Jun-yong-lee/Omok_robot/goboard_point_detect/result/img.jpg

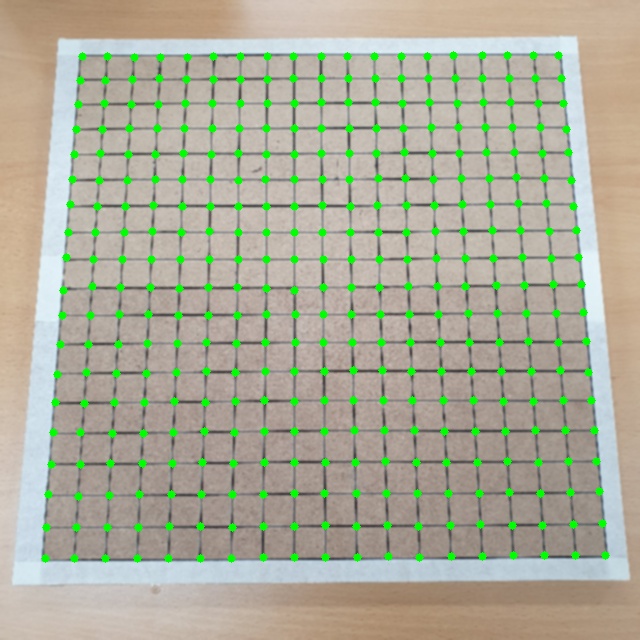
goboard_point_detect/result/img.jpg
