Jun-yong-lee/Omok_robot/goboard_point_detect/result/labeled_in_order.jpg

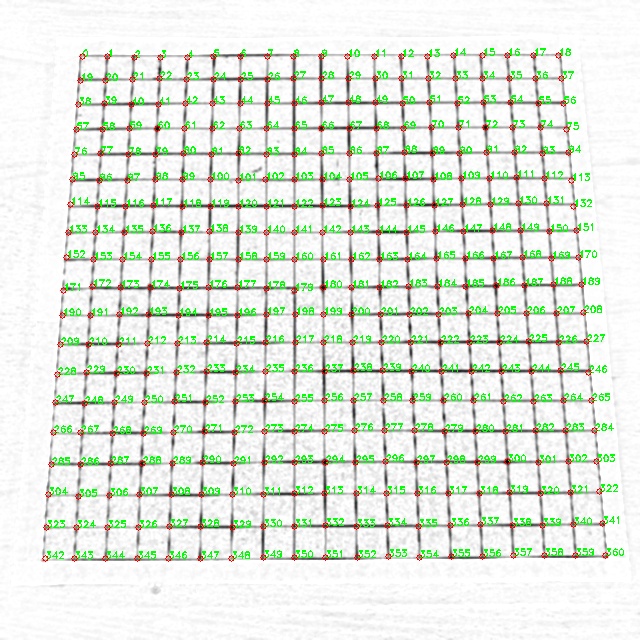
goboard_point_detect/result/labeled_in_order.jpg
