Jun-yong-lee/Omok_robot/goboard_point_detect/goboard2.jpg

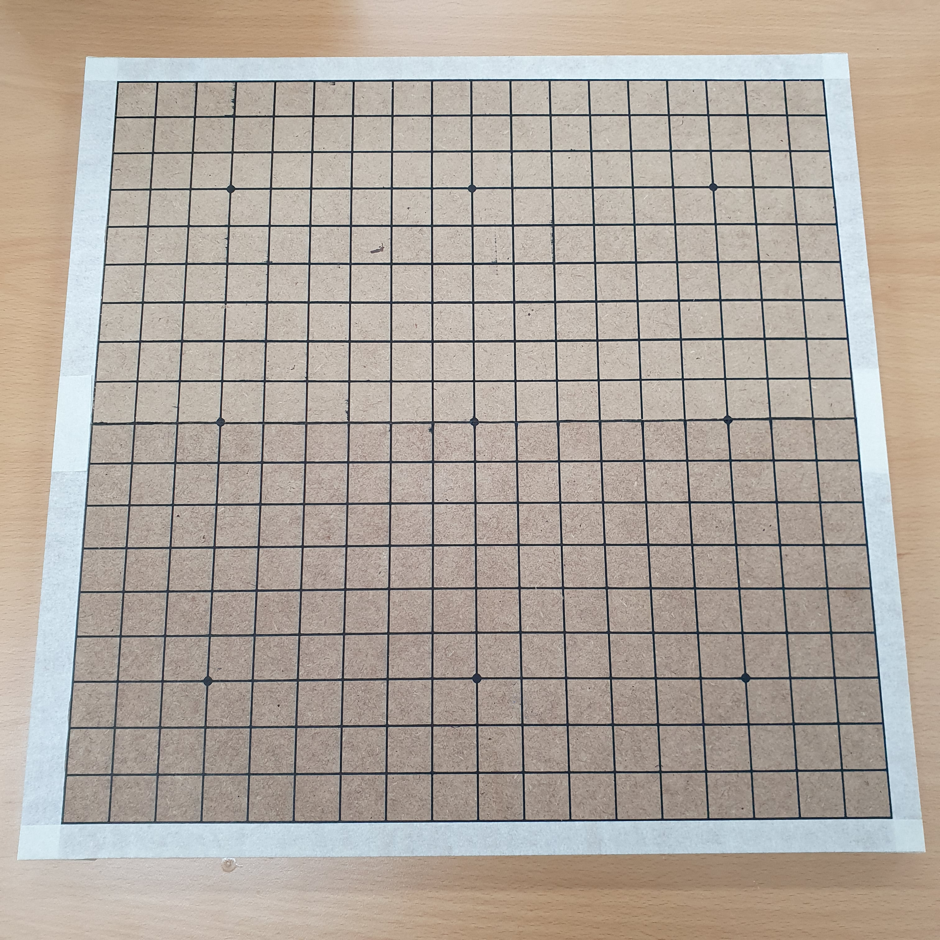
goboard_point_detect/goboard2.jpg
