Jun-yong-lee/Omok_robot/design_board_box/치수 늘린 모터 케이스/치수_solenoide fixed line.SLDPRT

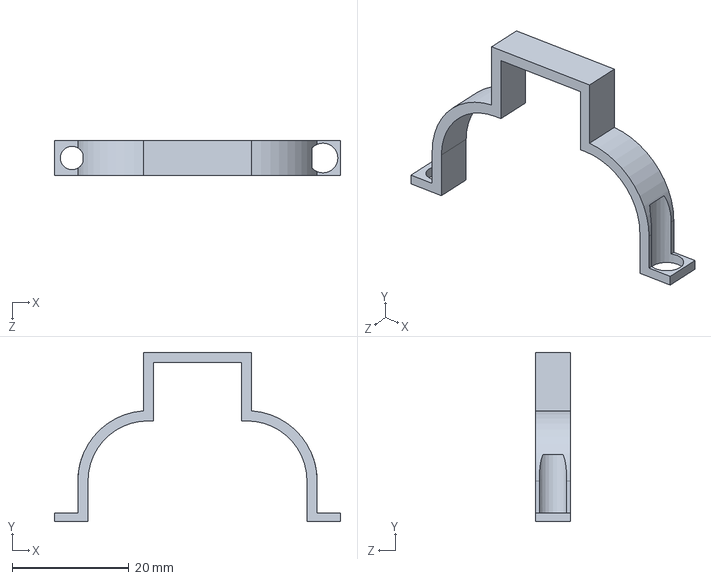
[picture p18: CAD file, 2022-11-21, last stored version]
design_board_box/치수 늘린 모터 케이스/치수_solenoide fixed line.SLDPRT
49.0 x 29.0 x 6.00 mm
