Jun-yong-lee/Omok_robot/design_dispenser/알.SLDPRT

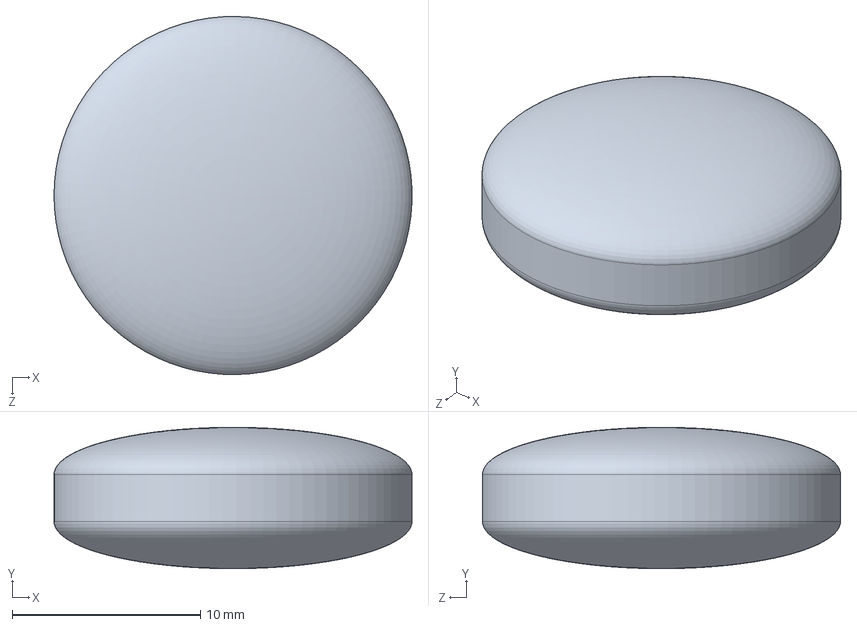
[picture p19: CAD file, 2022-11-21, last stored version]
design_dispenser/알.SLDPRT
19.0 x 7.50 x 19.0 mm
