Jun-yong-lee/Omok_robot/design_place/Profile link.SLDPRT

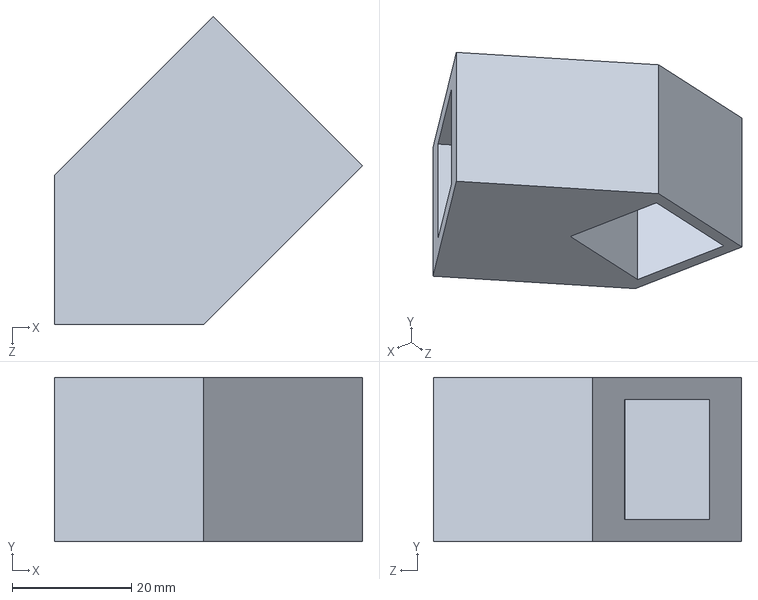
[picture p20: CAD file, 2022-11-21, last stored version]
design_place/Profile link.SLDPRT
51.6 x 27.5 x 51.6 mm
