Jun-yong-lee/Omok_robot/design_place/DP2020_420mm.SLDPRT

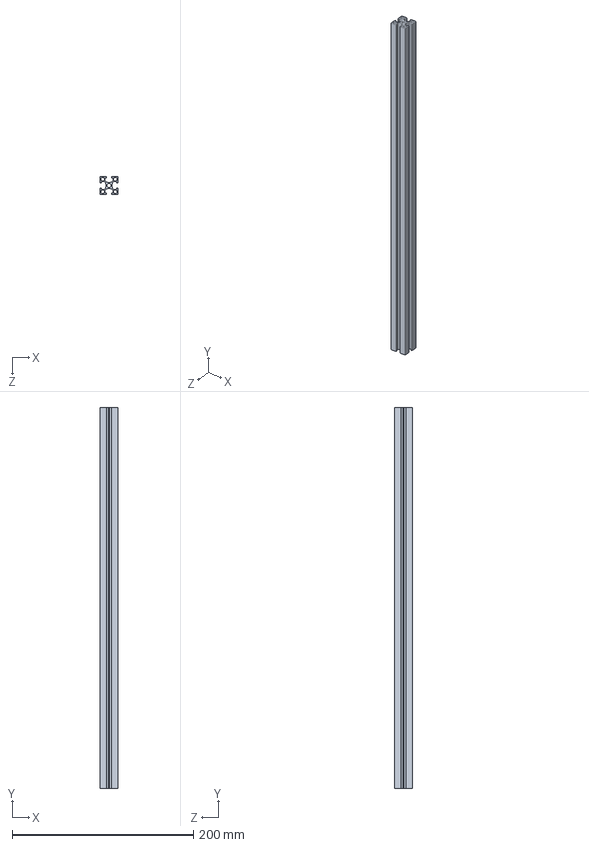
[picture p21: CAD file, 2022-11-21, last stored version]
design_place/DP2020_420mm.SLDPRT
20.0 x 420.0 x 20.0 mm
