Jun-yong-lee/Omok_robot/design_board_box/Vacuum Pump case 상.SLDPRT

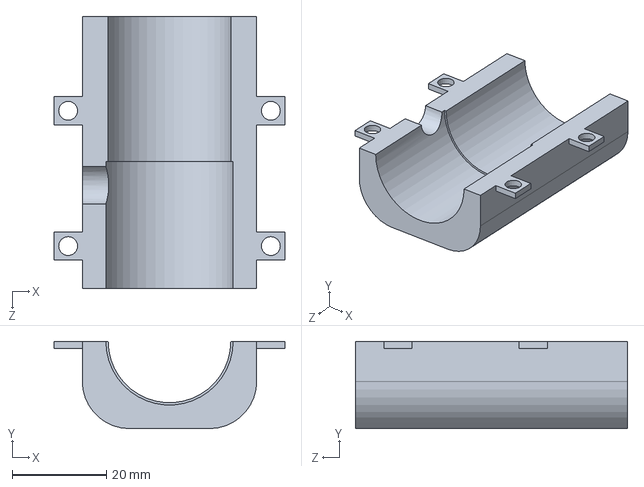
[picture p22: CAD file, 2022-11-21, last stored version]
design_board_box/Vacuum Pump case 상.SLDPRT
49.0 x 18.5 x 57.7 mm
