Jun-yong-lee/Omok_robot/design_dispenser/SG90.SLDPRT

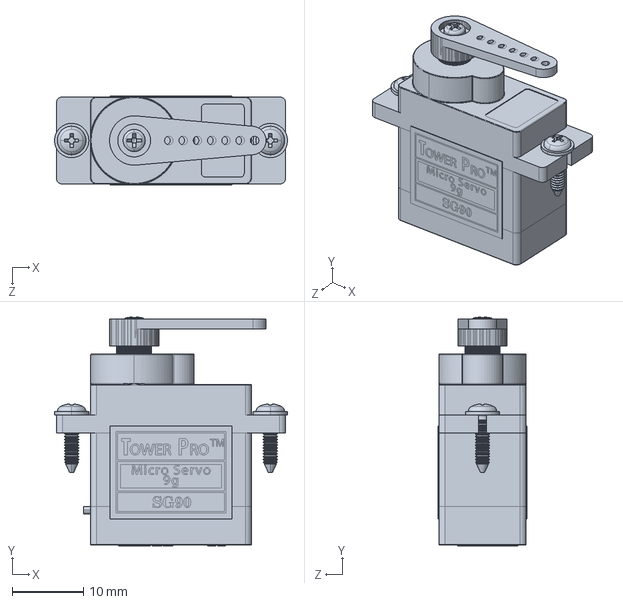
[picture p23: CAD file, 2022-11-21, last stored version]
design_dispenser/SG90.SLDPRT
32.6 x 32.0 x 12.4 mm
