Jun-yong-lee/Omok_robot/design_place/DP2020_510mm.SLDPRT

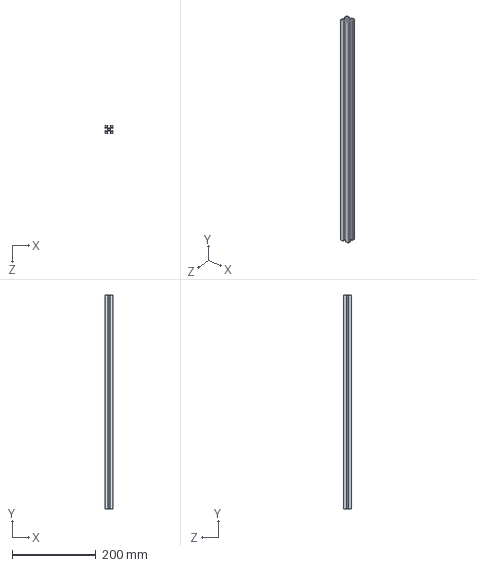
[picture p24: CAD file, 2022-11-21, last stored version]
design_place/DP2020_510mm.SLDPRT
20.0 x 510.0 x 20.0 mm
