Jun-yong-lee/Omok_robot/design_dispenser/Motor fixed flat.SLDPRT

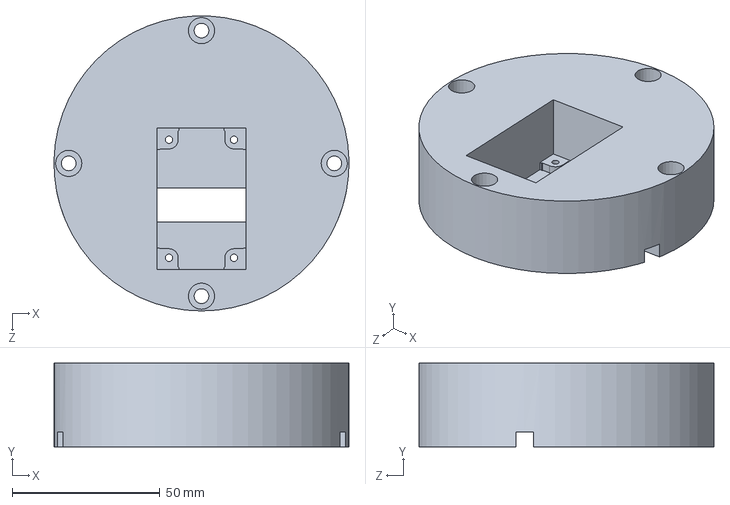
[picture p25: CAD file, 2022-11-21, last stored version]
design_dispenser/Motor fixed flat.SLDPRT
100.0 x 28.3 x 99.9 mm
