Jun-yong-lee/Omok_robot/design_place/Checkerboard.SLDPRT

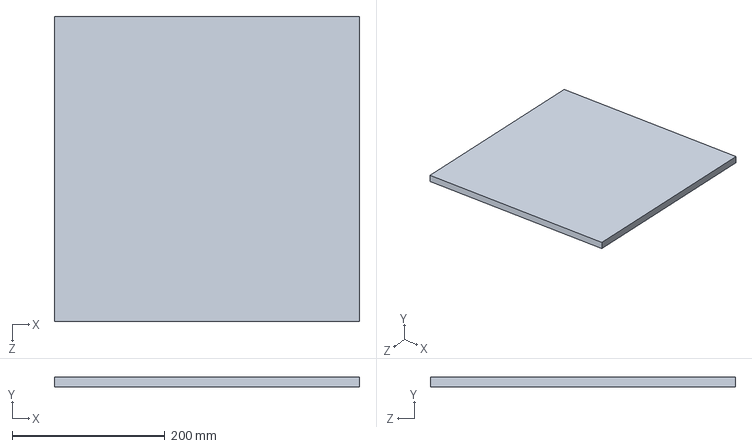
[picture p26: CAD file, 2022-11-21, last stored version]
design_place/Checkerboard.SLDPRT
400.0 x 13.0 x 400.0 mm
