Jun-yong-lee/Omok_robot/design_place/Cart.SLDPRT

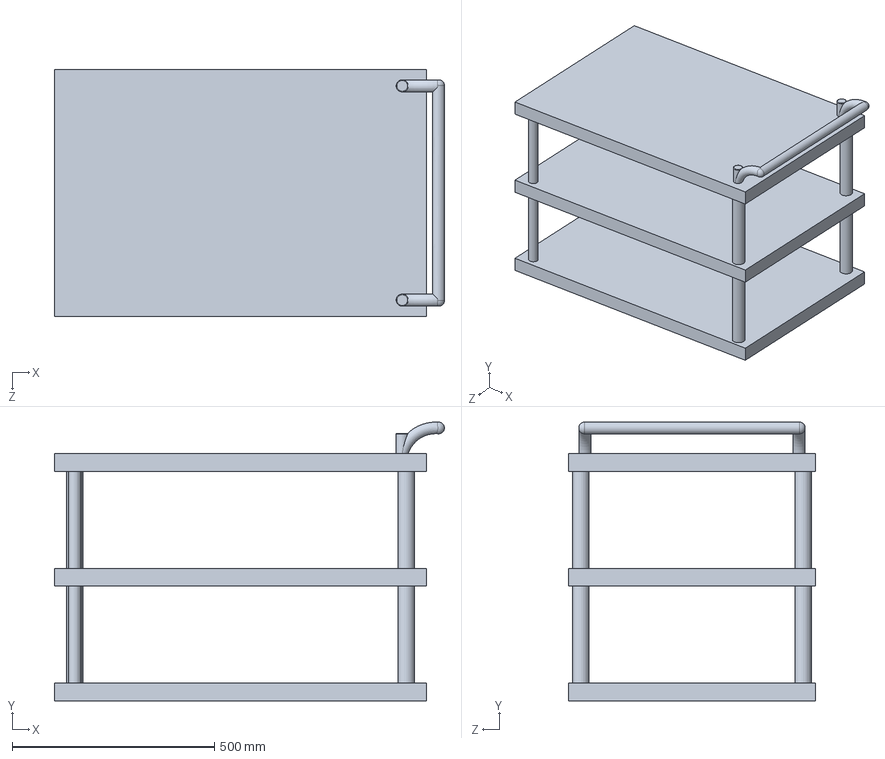
[picture p27: CAD file, 2022-11-21, last stored version]
design_place/Cart.SLDPRT
964.6 x 689.7 x 610.0 mm
