Jun-yong-lee/Omok_robot/design_board_box/solenoide.SLDPRT

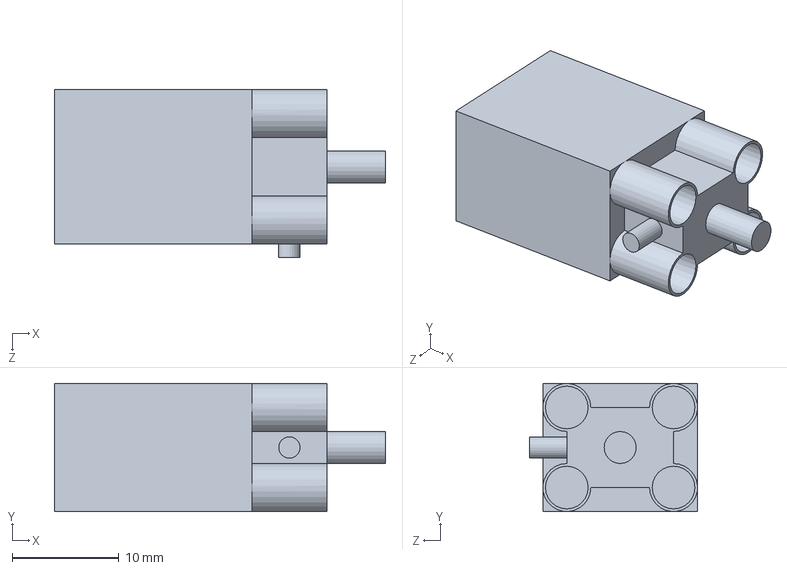
[picture p28: CAD file, 2022-11-21, last stored version]
design_board_box/solenoide.SLDPRT
31.0 x 12.0 x 15.8 mm
