Jun-yong-lee/Omok_robot/design_dispenser/오목알 경사각 증가 및 입구 확장.SLDPRT

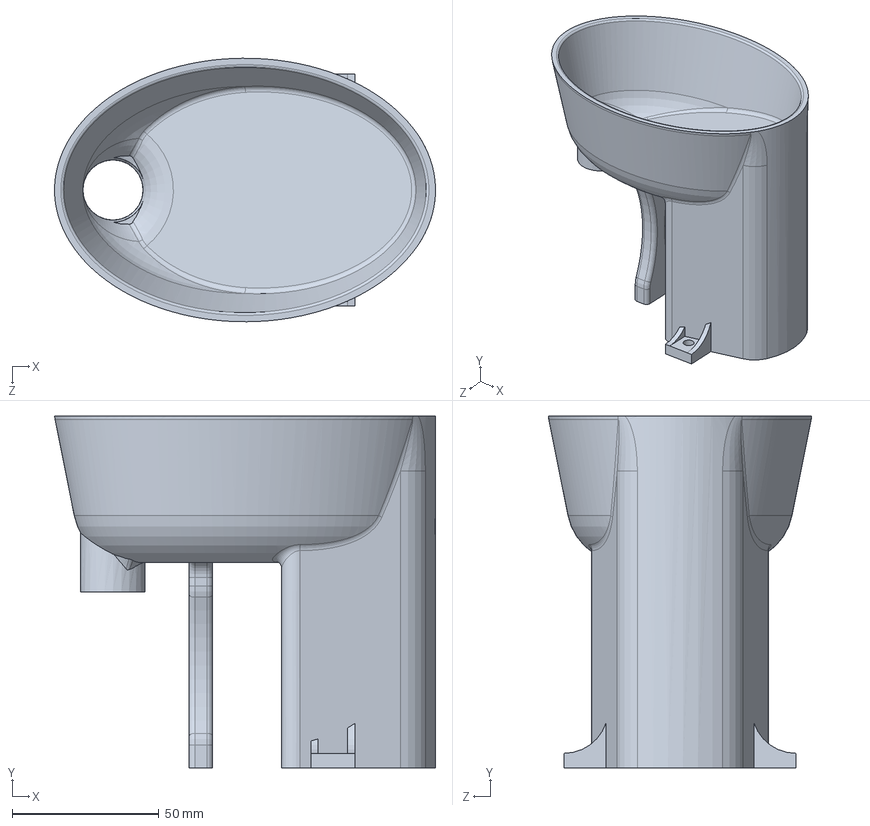
[picture p29: CAD file, 2022-11-21, last stored version]
design_dispenser/오목알 경사각 증가 및 입구 확장.SLDPRT
129.9 x 120.0 x 89.9 mm
