Jun-yong-lee/Omok_robot/design_place/DP2020_200mm.SLDPRT

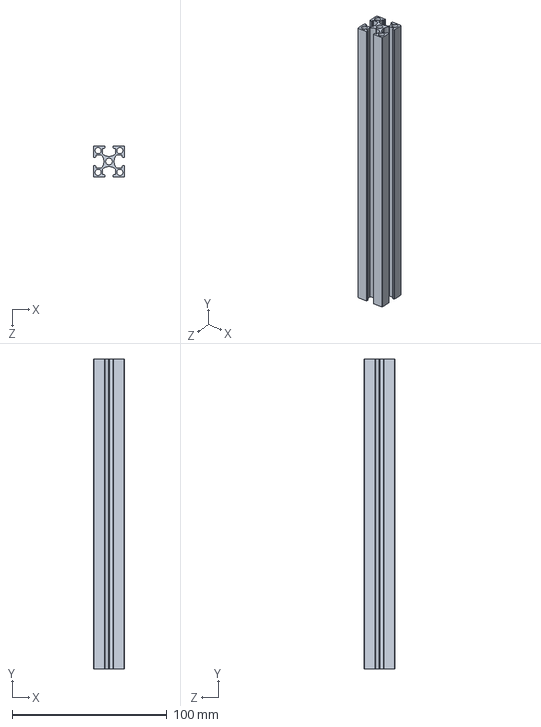
[picture p30: CAD file, 2022-11-21, last stored version]
design_place/DP2020_200mm.SLDPRT
20.0 x 200.0 x 20.0 mm
