Jun-yong-lee/Omok_robot/design_board_box/Vacuum Pump.SLDPRT

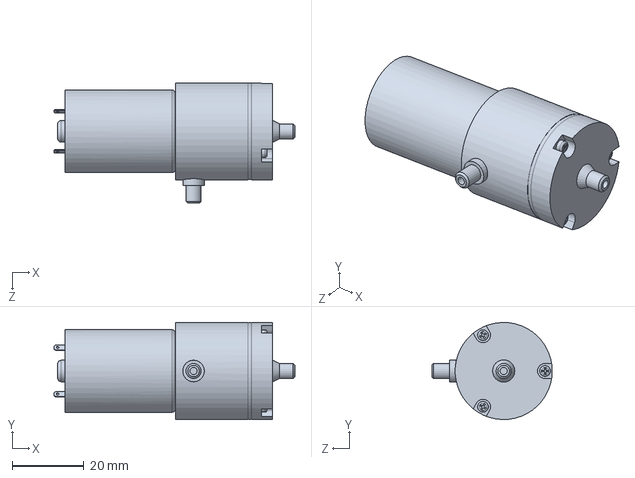
[picture p31: CAD file, 2022-11-21, last stored version]
design_board_box/Vacuum Pump.SLDPRT
67.0 x 27.0 x 33.5 mm
