Jun-yong-lee/Omok_robot/design_board_box/board support_L30.SLDPRT

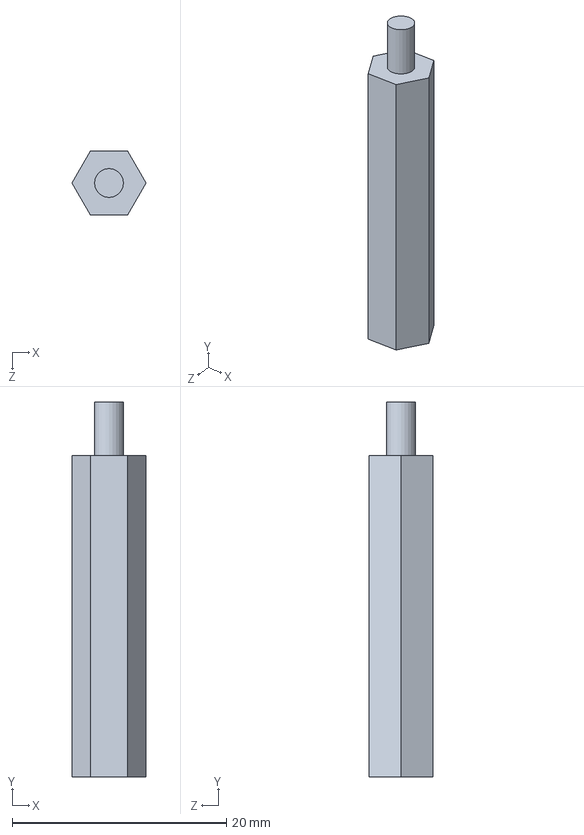
[picture p32: CAD file, 2022-11-21, last stored version]
design_board_box/board support_L30.SLDPRT
6.93 x 35.0 x 6.00 mm
