Jun-yong-lee/Omok_robot/design_board_box/Arduino uno.SLDPRT

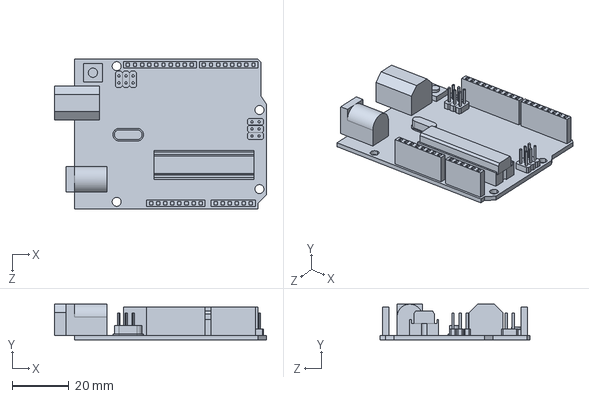
[picture p33: CAD file, 2022-11-21, last stored version]
design_board_box/Arduino uno.SLDPRT
75.0 x 12.6 x 53.0 mm
