Jun-yong-lee/Omok_robot/design_board_box/1 plate.SLDPRT

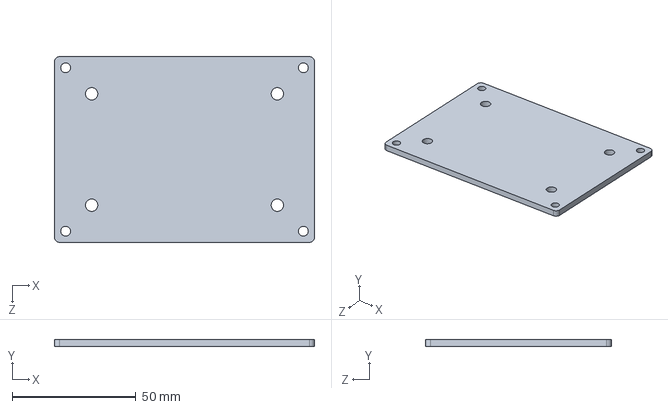
[picture p34: CAD file, 2022-11-21, last stored version]
design_board_box/1 plate.SLDPRT
105.0 x 3.00 x 75.0 mm
