Jun-yong-lee/Omok_robot/design_board_box/board support_L5.SLDPRT

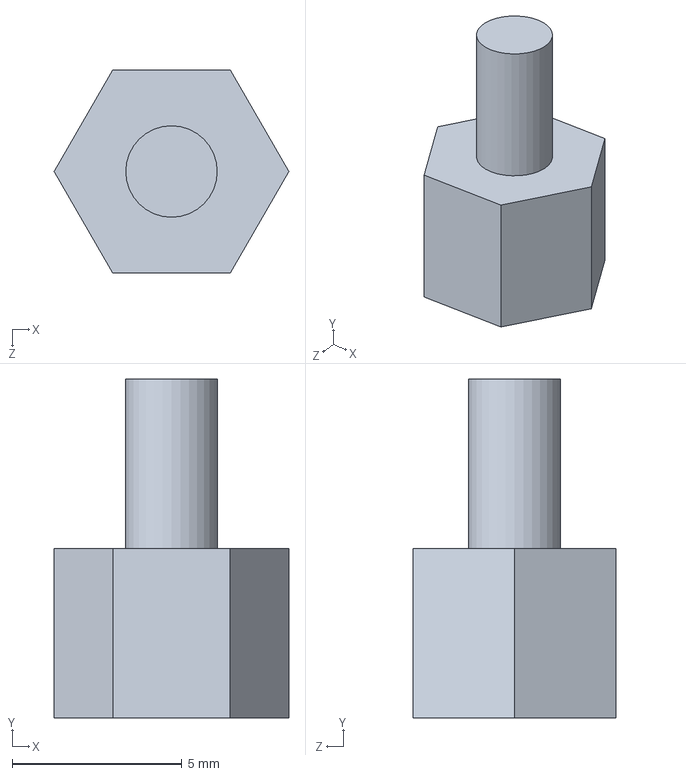
[picture p36: CAD file, 2022-11-21, last stored version]
design_board_box/board support_L5.SLDPRT
6.93 x 10.0 x 6.00 mm
