Jun-yong-lee/Omok_robot/design_board_box/Sensor Board.SLDPRT

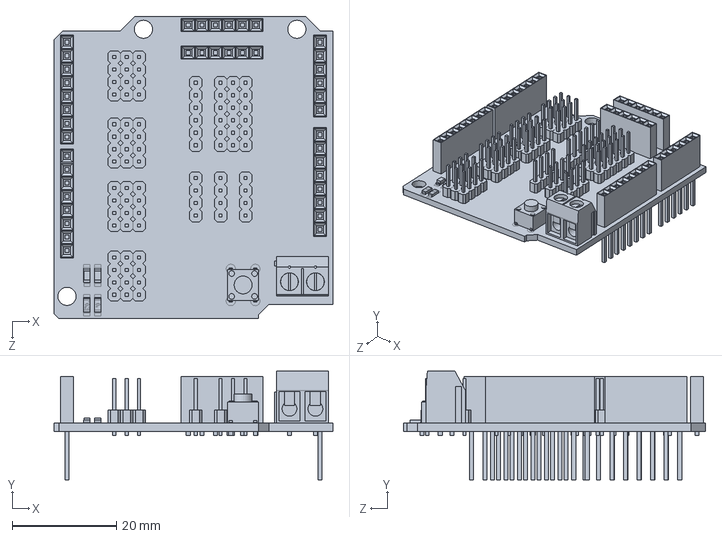
[picture p37: CAD file, 2022-11-21, last stored version]
design_board_box/Sensor Board.SLDPRT
53.6 x 20.9 x 58.2 mm
