Jun-yong-lee/Omok_robot/goboard_point_detect/result/closex.jpg

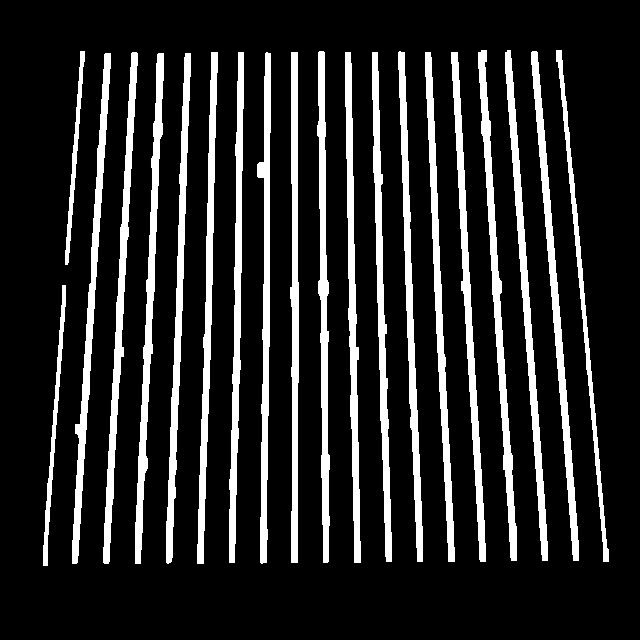
goboard_point_detect/result/closex.jpg
