Jun-yong-lee/Omok_robot/goboard_point_detect/result/closey.jpg

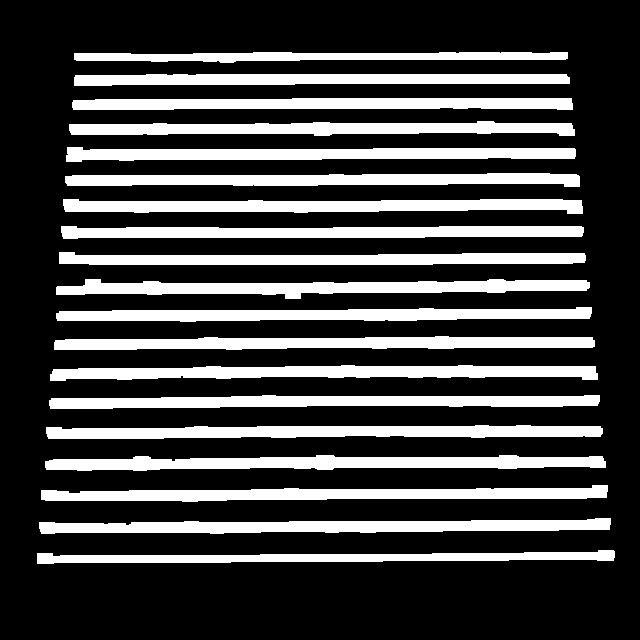
goboard_point_detect/result/closey.jpg
