Jun-yong-lee/Omok_robot/goboard_point_detect/result/res2.jpg

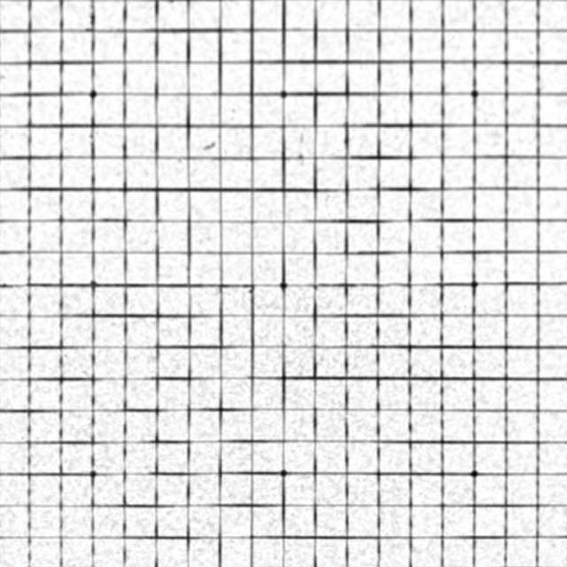
goboard_point_detect/result/res2.jpg
